JLeseur/DU-UAV-Underwater-Submersible/SolidWorks/Internals/Battery Assumbley.SLDASM

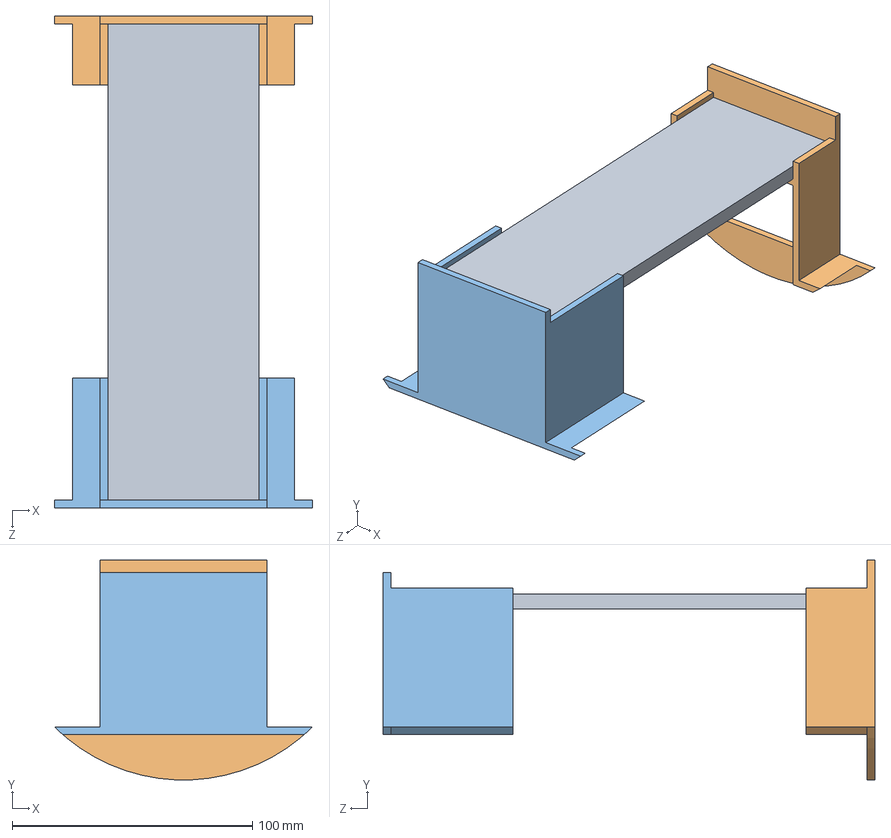
[picture p3: CAD file, 2024-06-05]
SolidWorks/Internals/Battery Assumbley.SLDASM
107.3 x 91.4 x 204.5 mm
Battery Mount Back
Battery Mount Front
Battery Weight
