JLeseur/DU-UAV-Underwater-Submersible/SolidWorks/Ballast Tank/Off The Self/Ballast Pipe Joint [2in PVC Coupling].SLDPRT

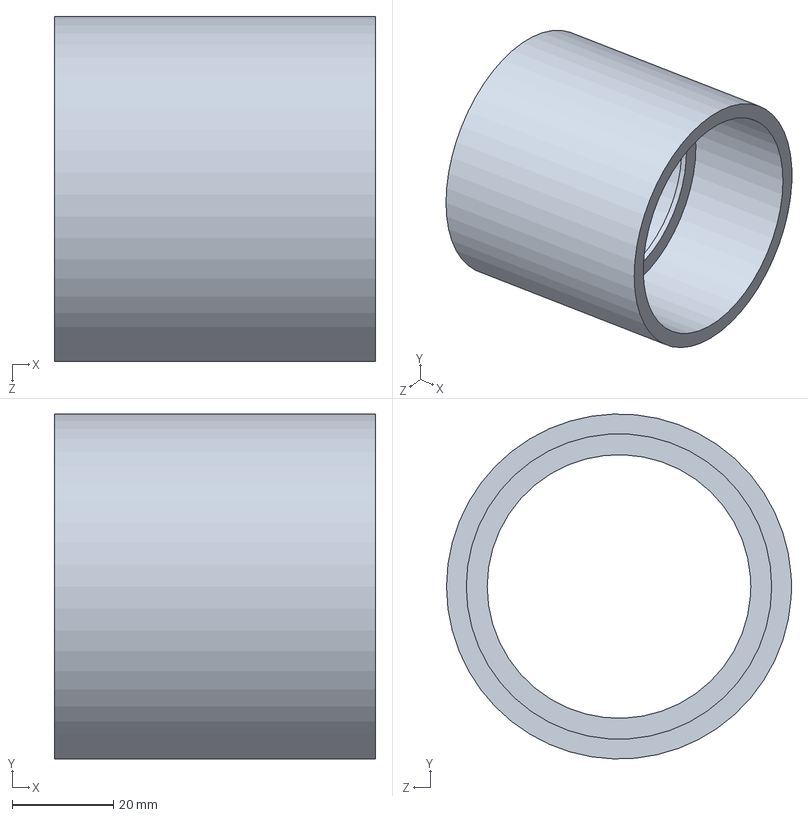
[picture p14: CAD file, 2024-06-05]
SolidWorks/Ballast Tank/Off The Self/Ballast Pipe Joint [2in PVC Coupling].SLDPRT
63.5 x 68.1 x 68.1 mm
