JLeseur/DU-UAV-Underwater-Submersible/SolidWorks/Hull/Custom Fabrication/Small Weight.SLDPRT

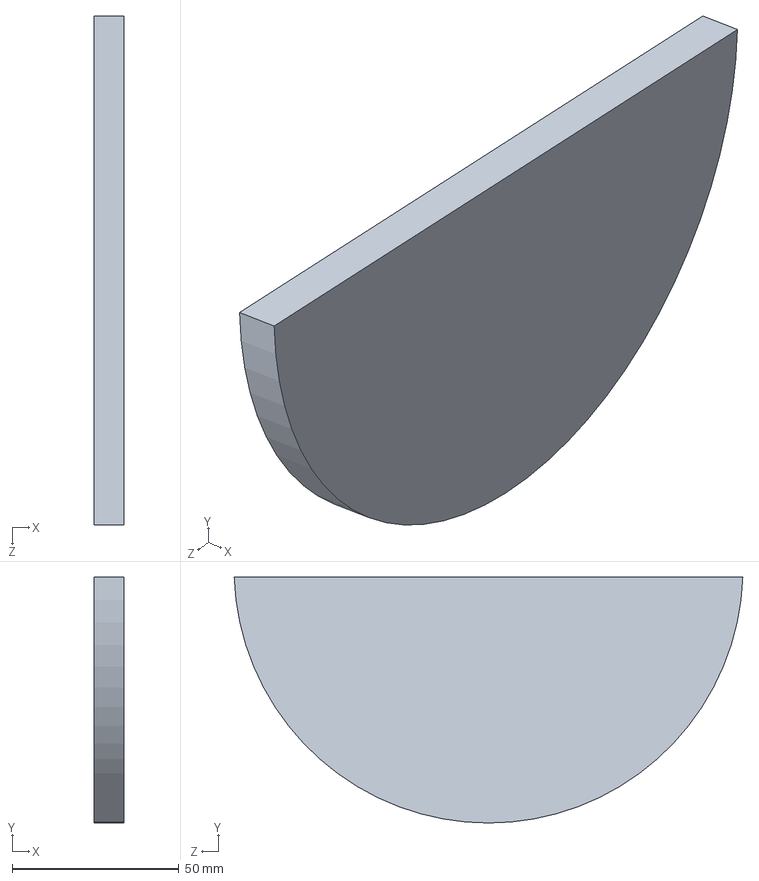
[picture p15: CAD file, 2024-06-05]
SolidWorks/Hull/Custom Fabrication/Small Weight.SLDPRT
8.89 x 73.7 x 152.3 mm
