JLeseur/DU-UAV-Underwater-Submersible/SolidWorks/Internals/Custom Fabrication/Bottom Tray.SLDPRT

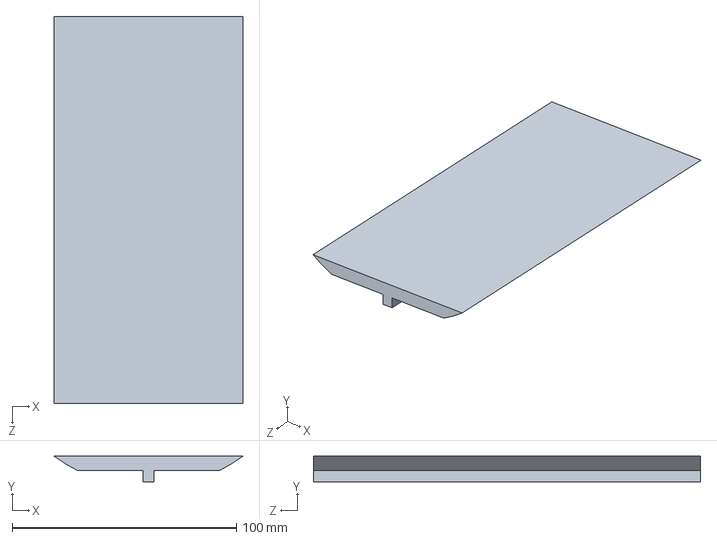
[picture p16: CAD file, 2024-06-05]
SolidWorks/Internals/Custom Fabrication/Bottom Tray.SLDPRT
84.3 x 11.4 x 172.7 mm
