JLeseur/DU-UAV-Underwater-Submersible/SolidWorks/Ballast Tank/Custom Fabrication/Gear Key.SLDPRT

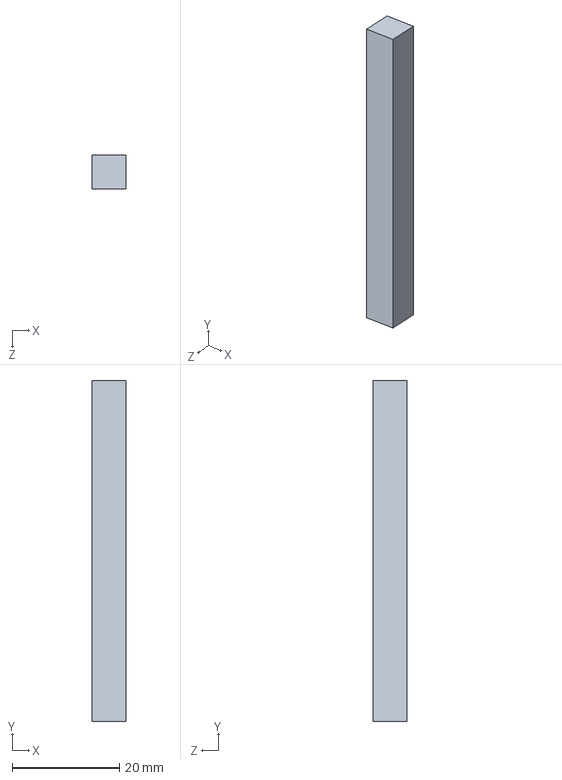
[picture p17: CAD file, 2024-06-05]
SolidWorks/Ballast Tank/Custom Fabrication/Gear Key.SLDPRT
6.35 x 63.5 x 6.35 mm
