JLeseur/DU-UAV-Underwater-Submersible/SolidWorks/Ballast Tank/Off The Self/Lower Ballast Pipe [2in PVC Pipe].SLDPRT

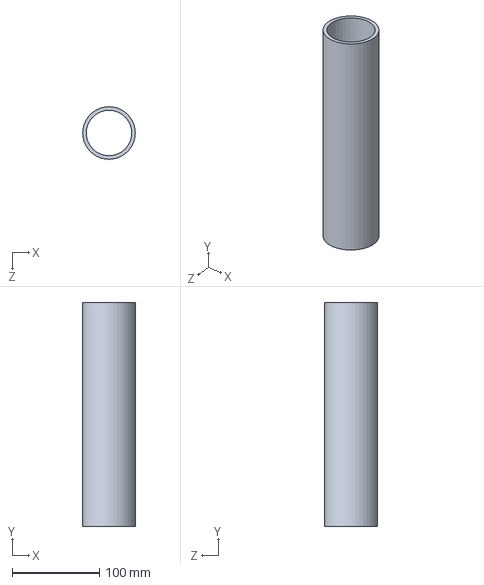
[picture p18: CAD file, 2024-06-05]
SolidWorks/Ballast Tank/Off The Self/Lower Ballast Pipe [2in PVC Pipe].SLDPRT
60.3 x 256.6 x 60.3 mm
