JLeseur/DU-UAV-Underwater-Submersible/SolidWorks/Hull/Custom Fabrication/Cross Member Clamp.SLDPRT

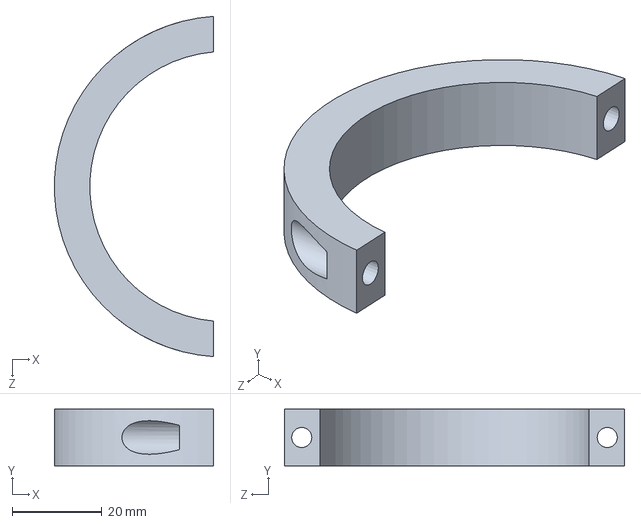
[picture p19: CAD file, 2024-06-05]
SolidWorks/Hull/Custom Fabrication/Cross Member Clamp.SLDPRT
35.5 x 12.7 x 76.0 mm
