JLeseur/DU-UAV-Underwater-Submersible/SolidWorks/Internals/Custom Fabrication/Middle Plate.SLDPRT

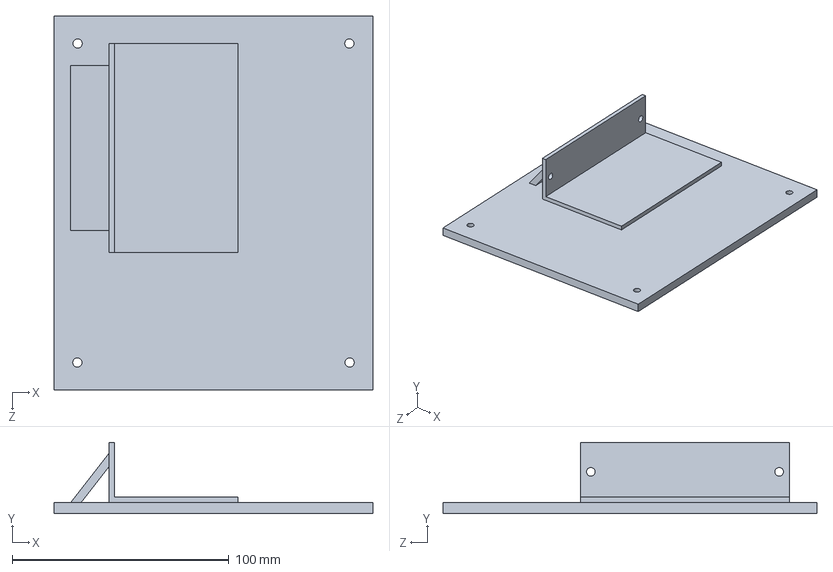
[picture p20: CAD file, 2024-06-05]
SolidWorks/Internals/Custom Fabrication/Middle Plate.SLDPRT
147.3 x 33.0 x 172.7 mm
