JLeseur/DU-UAV-Underwater-Submersible/SolidWorks/Ballast Tank/Custom Fabrication/Drive Shaft.SLDPRT

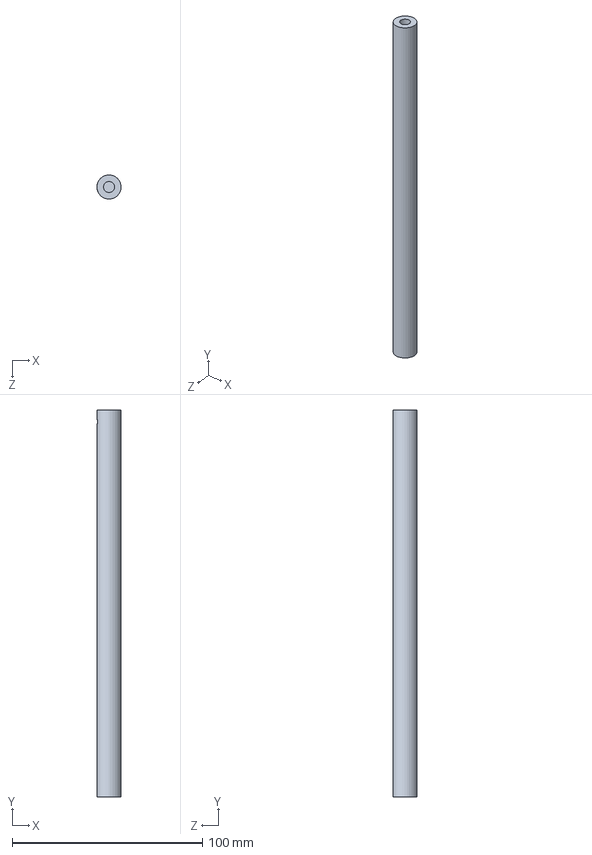
[picture p21: CAD file, 2024-06-05]
SolidWorks/Ballast Tank/Custom Fabrication/Drive Shaft.SLDPRT
12.7 x 203.2 x 12.7 mm
