JLeseur/DU-UAV-Underwater-Submersible/SolidWorks/Hull/Custom Fabrication/Cross Memeber.SLDPRT

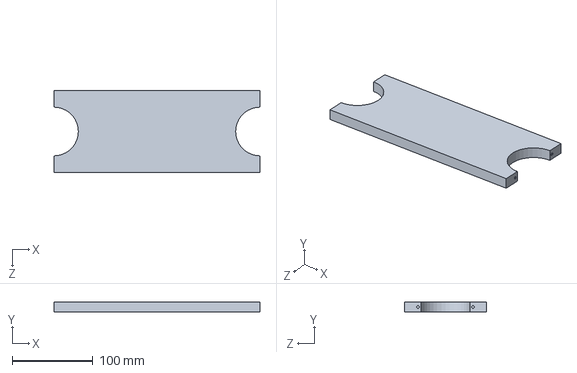
[picture p22: CAD file, 2024-06-05]
SolidWorks/Hull/Custom Fabrication/Cross Memeber.SLDPRT
255.3 x 12.7 x 101.6 mm
