JLeseur/DU-UAV-Underwater-Submersible/SolidWorks/Ballast Tank/Custom Fabrication/Gear Box.SLDPRT

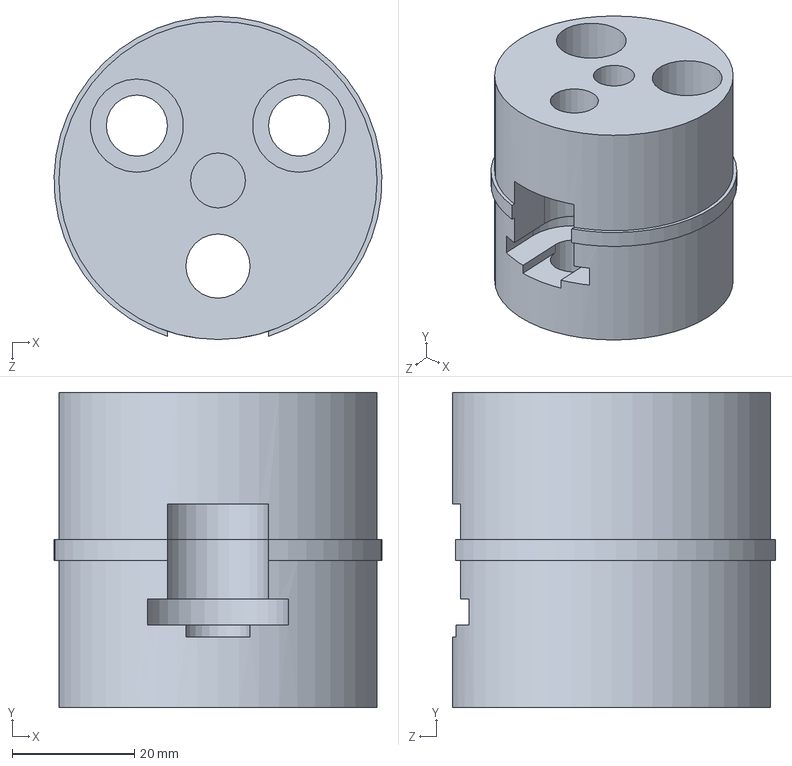
[picture p23: CAD file, 2024-06-05]
SolidWorks/Ballast Tank/Custom Fabrication/Gear Box.SLDPRT
53.6 x 51.5 x 52.8 mm
