JLeseur/DU-UAV-Underwater-Submersible/SolidWorks/Ballast Tank/Off The Self/Motor Housing Cap [3in PVC End Cap].SLDPRT

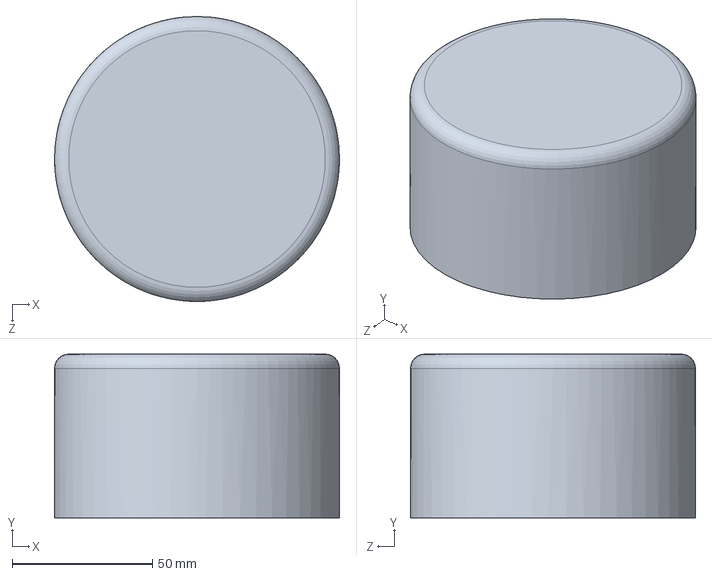
[picture p24: CAD file, 2024-06-05]
SolidWorks/Ballast Tank/Off The Self/Motor Housing Cap [3in PVC End Cap].SLDPRT
101.6 x 58.4 x 101.6 mm
