JLeseur/DU-UAV-Underwater-Submersible/SolidWorks/Hull/Custom Fabrication/Large Weight.SLDPRT

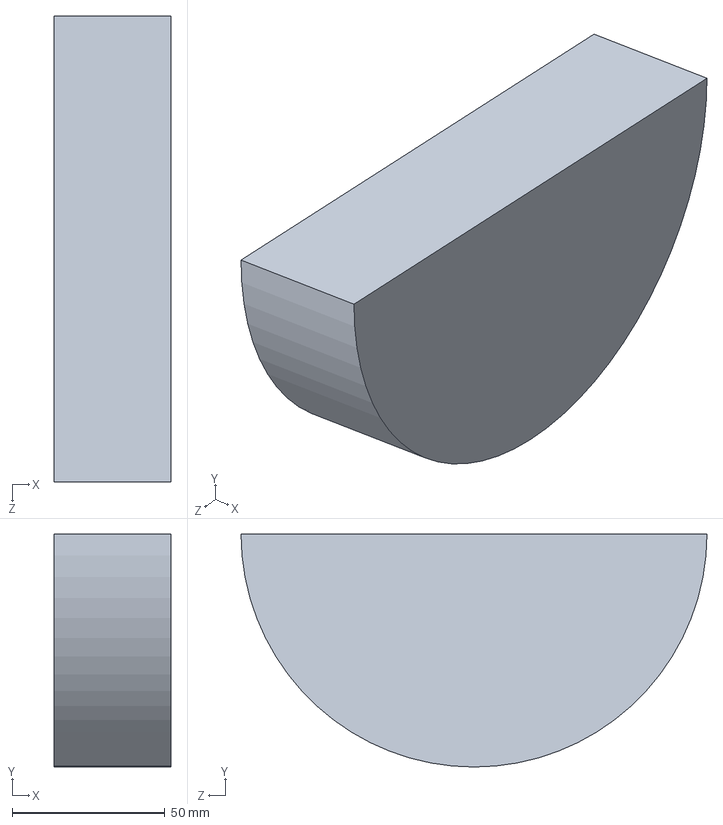
[picture p25: CAD file, 2024-06-05]
SolidWorks/Hull/Custom Fabrication/Large Weight.SLDPRT
38.1 x 76.2 x 152.4 mm
