JLeseur/DU-UAV-Underwater-Submersible/SolidWorks/Internals/Custom Fabrication/End Bracket.SLDPRT

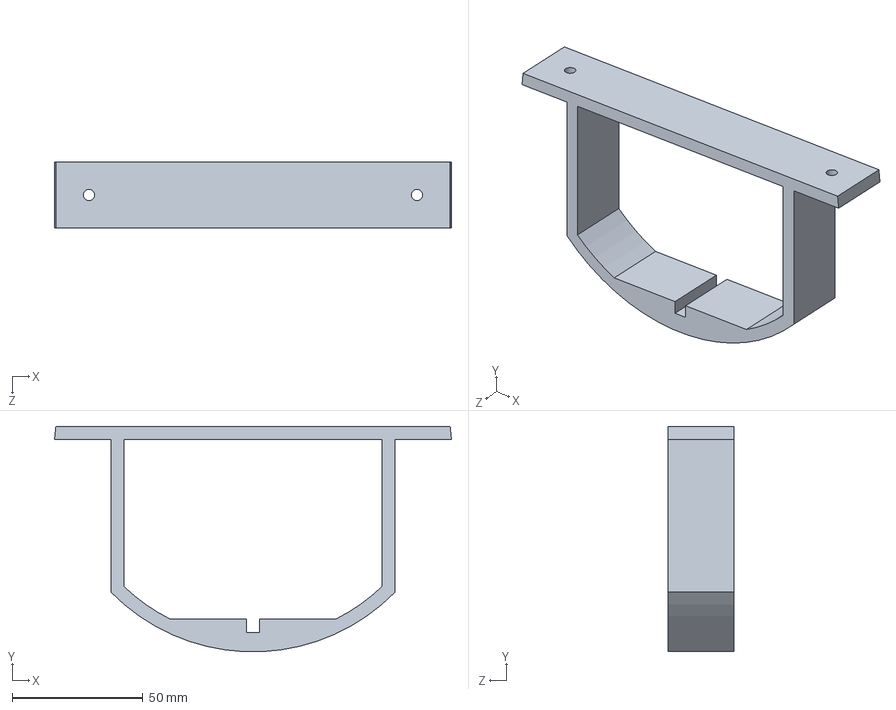
[picture p26: CAD file, 2024-06-05]
SolidWorks/Internals/Custom Fabrication/End Bracket.SLDPRT
152.1 x 86.3 x 25.4 mm
