JLeseur/DU-UAV-Underwater-Submersible/SolidWorks/Ballast Tank/Custom Fabrication/Drive Gear.SLDPRT

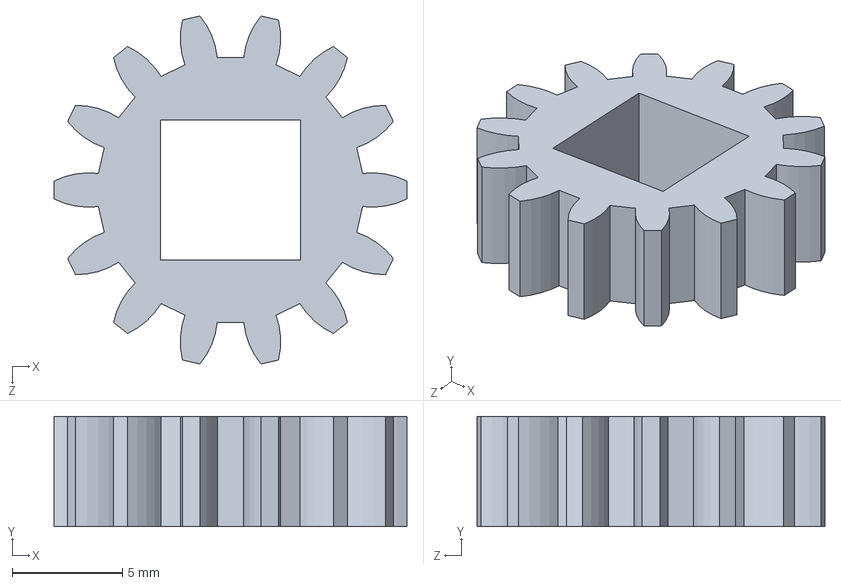
[picture p27: CAD file, 2024-06-05]
SolidWorks/Ballast Tank/Custom Fabrication/Drive Gear.SLDPRT
16.0 x 5.00 x 15.8 mm
