JLeseur/DU-UAV-Underwater-Submersible/SolidWorks/Ballast Tank/Off The Self/Piston Seal [High-Speed Piston Seal for 2in Bore Diameter].SLDPRT

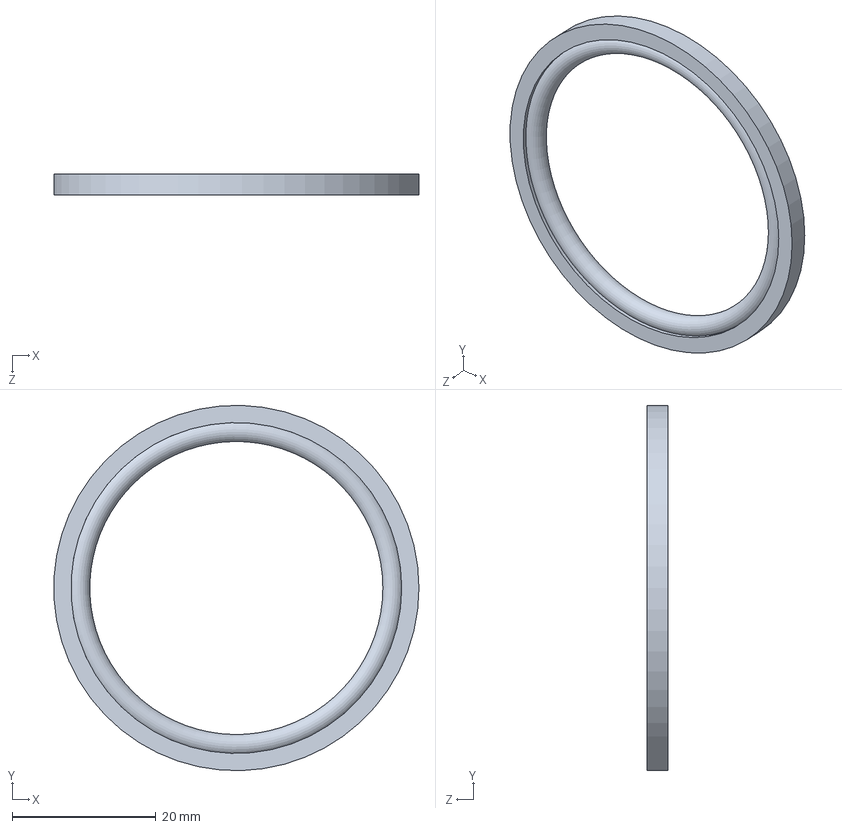
[picture p28: CAD file, 2024-06-05]
SolidWorks/Ballast Tank/Off The Self/Piston Seal [High-Speed Piston Seal for 2in Bore Diameter].SLDPRT
50.8 x 50.8 x 2.92 mm
