JLeseur/DU-UAV-Underwater-Submersible/SolidWorks/Hull/Custom Fabrication/Hull Clamp.SLDPRT

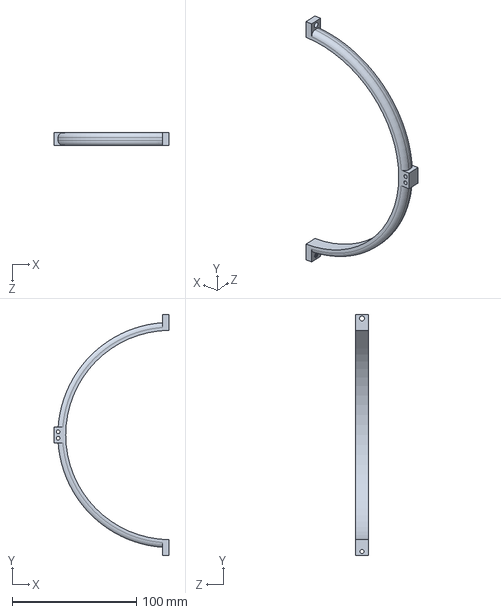
[picture p29: CAD file, 2024-06-05]
SolidWorks/Hull/Custom Fabrication/Hull Clamp.SLDPRT
92.2 x 193.7 x 10.2 mm
