JLeseur/DU-UAV-Underwater-Submersible/SolidWorks/Internals/Custom Fabrication/Middle Bracket.SLDPRT

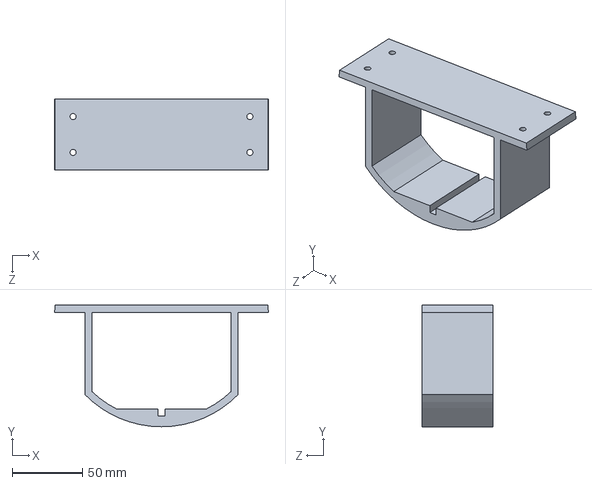
[picture p30: CAD file, 2024-06-05]
SolidWorks/Internals/Custom Fabrication/Middle Bracket.SLDPRT
152.1 x 86.4 x 50.8 mm
