JLeseur/DU-UAV-Underwater-Submersible/SolidWorks/Ballast Tank/Off The Self/Guide Rod [8mm Rod].SLDPRT

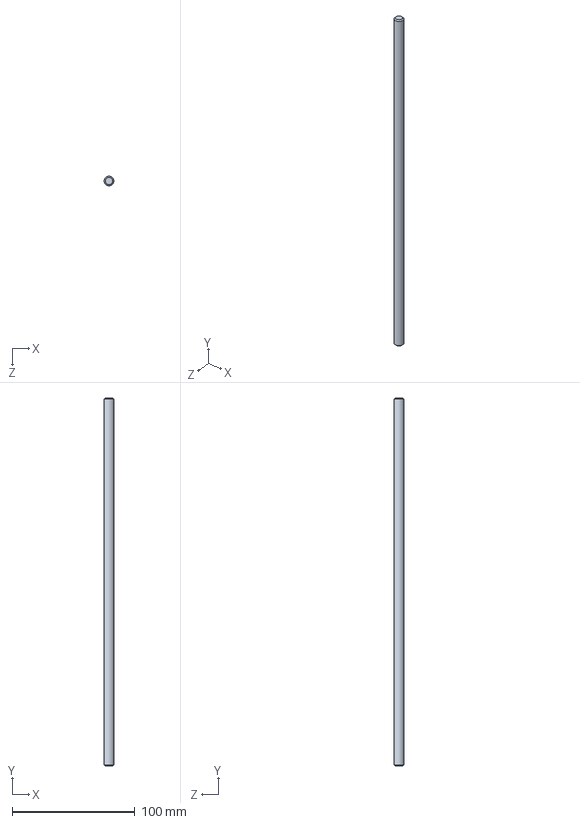
[picture p31: CAD file, 2024-06-05]
SolidWorks/Ballast Tank/Off The Self/Guide Rod [8mm Rod].SLDPRT
7.94 x 300.0 x 8.00 mm
