JLeseur/DU-UAV-Underwater-Submersible/SolidWorks/Internals/Custom Fabrication/Battery Mount Back.SLDPRT

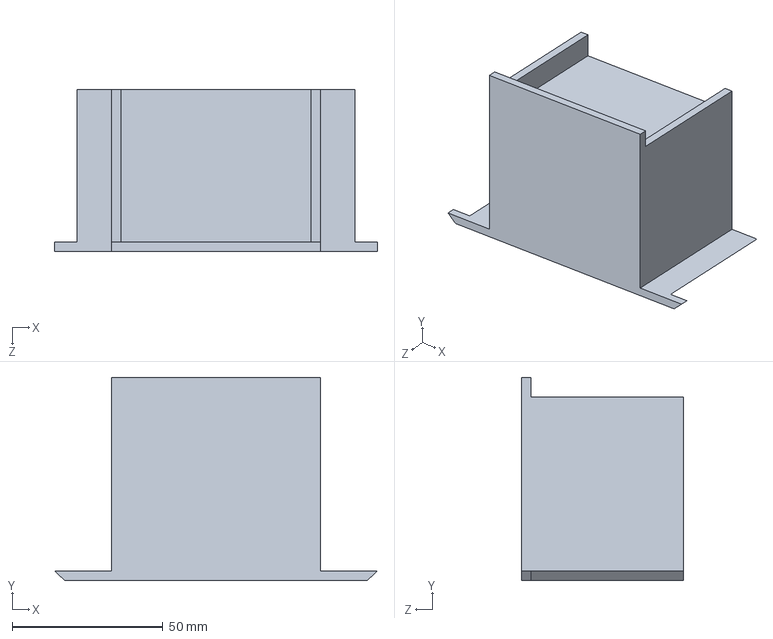
[picture p32: CAD file, 2024-06-05]
SolidWorks/Internals/Custom Fabrication/Battery Mount Back.SLDPRT
107.3 x 67.4 x 54.0 mm
