JLeseur/DU-UAV-Underwater-Submersible/SolidWorks/Ballast Tank/Off The Self/Linear Guide Bearing [LM8UU].SLDPRT

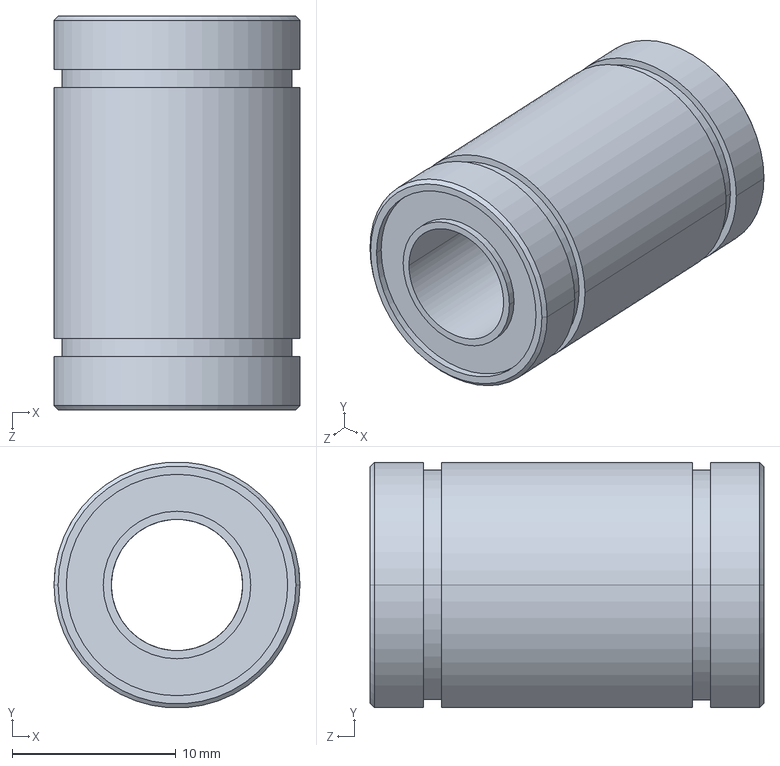
[picture p33: CAD file, 2024-06-05]
SolidWorks/Ballast Tank/Off The Self/Linear Guide Bearing [LM8UU].SLDPRT
15.0 x 15.0 x 24.0 mm
