JLeseur/DU-UAV-Underwater-Submersible/SolidWorks/Internals/Custom Fabrication/Battery Mount Front.SLDPRT

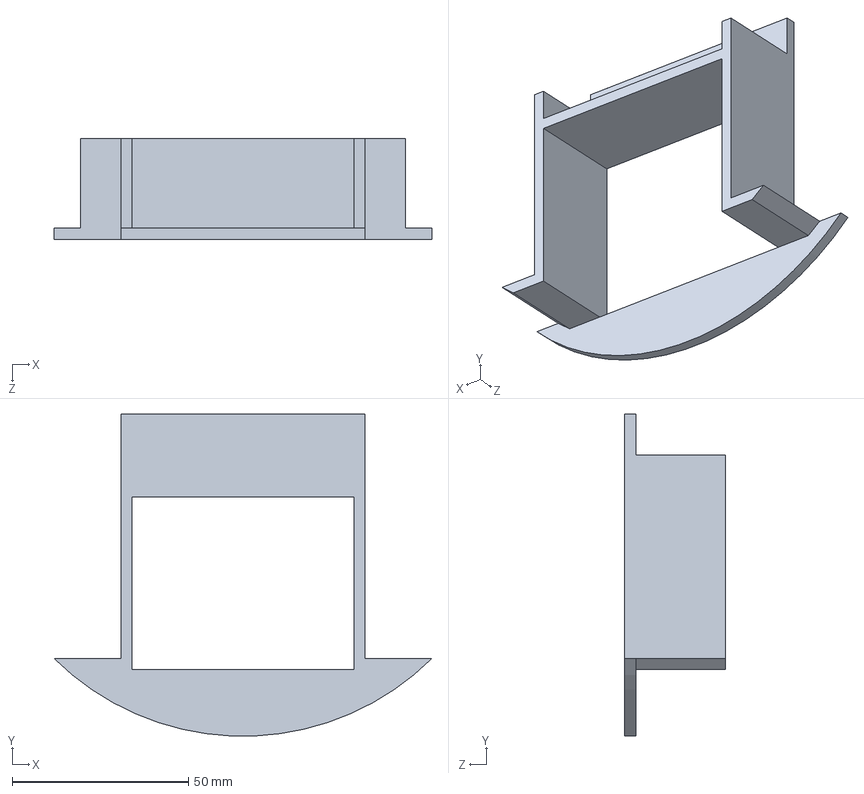
[picture p34: CAD file, 2024-06-05]
SolidWorks/Internals/Custom Fabrication/Battery Mount Front.SLDPRT
107.3 x 91.4 x 28.6 mm
