JLeseur/DU-UAV-Underwater-Submersible/SolidWorks/Ballast Tank/Off The Self/Motor Housing Opening [3in x 2in PVC Coupling].SLDPRT

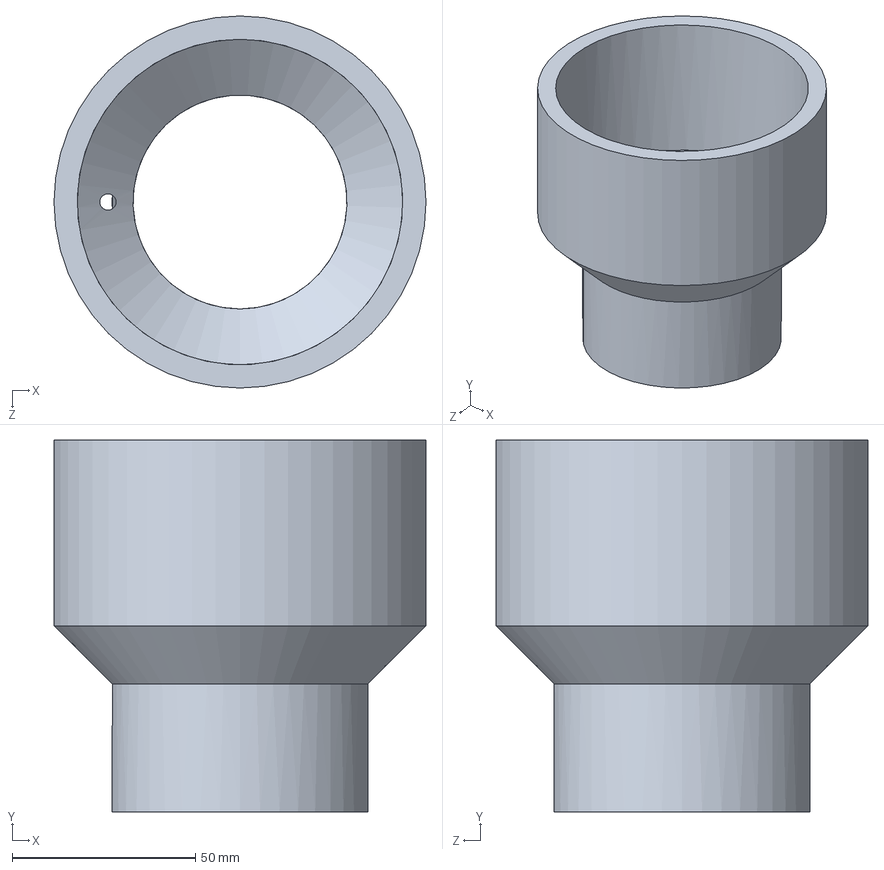
[picture p35: CAD file, 2024-06-05]
SolidWorks/Ballast Tank/Off The Self/Motor Housing Opening [3in x 2in PVC Coupling].SLDPRT
101.6 x 101.6 x 101.6 mm
