JLeseur/DU-UAV-Underwater-Submersible/SolidWorks/Ballast Tank/Piston.SLDASM

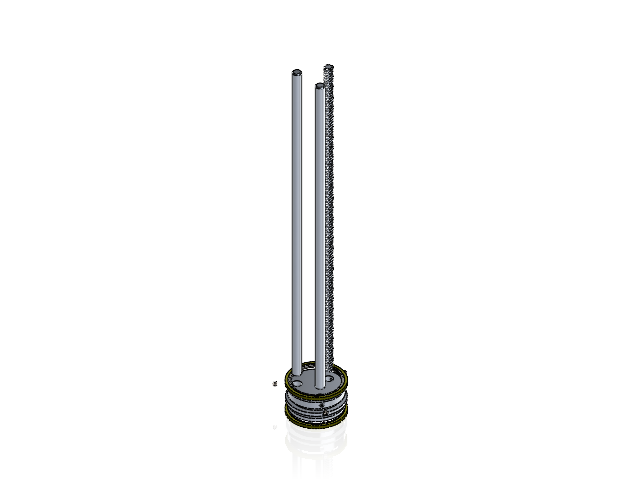
[picture p40: CAD file, 2024-06-05]
SolidWorks/Ballast Tank/Piston.SLDASM
Piston Head
Piston Seal [High-Speed Piston Seal for 2in Bore Diameter] x 2
Lead Screw [T8 4 Thread Lead Screw]
Guide Rod [8mm Rod] x 2
M4x0.7x4 Grub Screw x 3
