JLeseur/DU-UAV-Underwater-Submersible/SolidWorks/Hull/Clamps.SLDASM

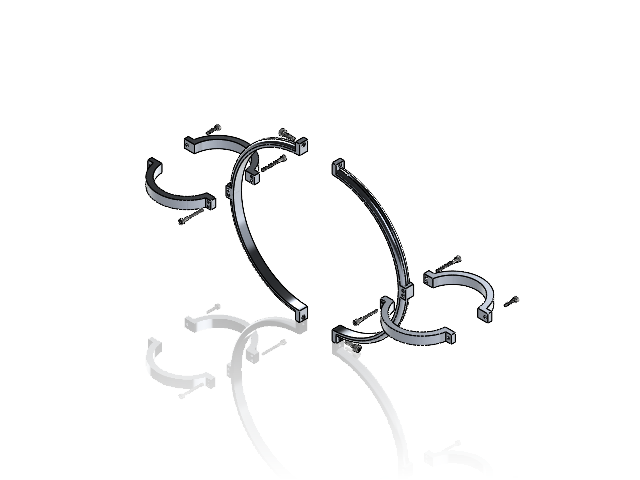
[picture p41: CAD file, 2024-06-05]
SolidWorks/Hull/Clamps.SLDASM
Hull Clamp x 2
Ballast Clamp With Threads x 2
Ballast Clamp x 2
M3x0.5x25 Screw x 4
M3x0.5x12 Screw x 2
M4x0.7x12 Screw x 2
