JLeseur/DU-UAV-Underwater-Submersible/SolidWorks/Ballast Tank/Motor Housing.SLDASM

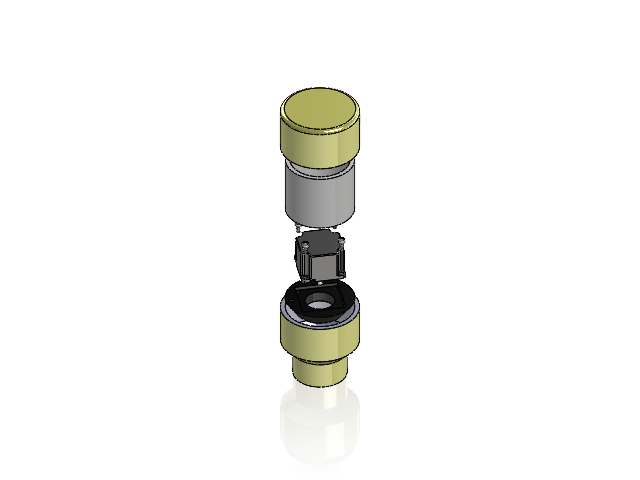
[picture p42: CAD file, 2024-06-05]
SolidWorks/Ballast Tank/Motor Housing.SLDASM
Motor Housing Cap [3in PVC End Cap]
Motor Housing [3in PVC Pipe]
Motor Housing Opening [3in x 2in PVC Coupling]
Motor Mount
M5x0.8x10 Screw x 4
Motor [NEMA 23 Stepper Motor]
